unspecworks/gamma-omega/images/black-raspberry-pi-pico-pins.png

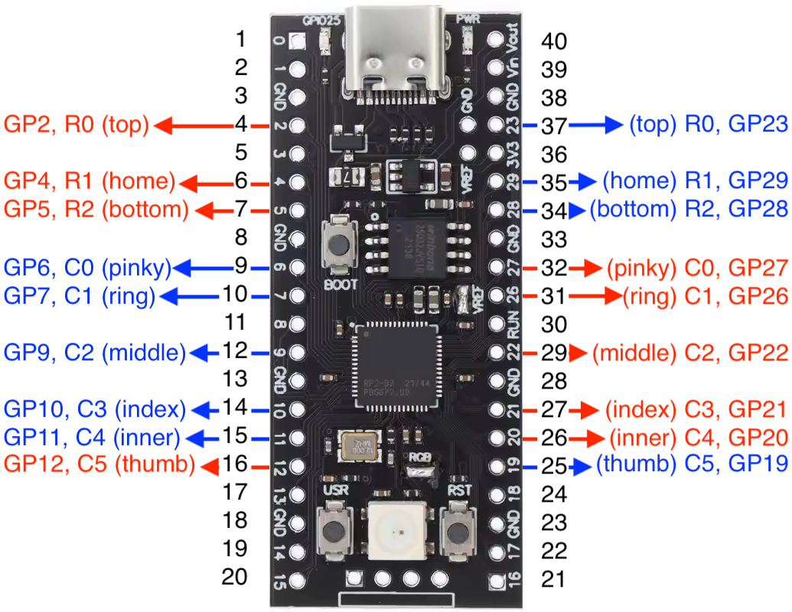
images/black-raspberry-pi-pico-pins.png
